RayPS/MacroPad/src/html.h

#ifndef HTML_H
#define HTML_H

#include <Arduino.h>

#define html_len 80776

const uint8_t html[] PROGMEM = {
0x1f,0x8b,0x08,0x00,0x00,0x00,0x00,0x00,0x02,0x13,0xcc,0xbd,0x69,0x73,0xdb,0xb8,0xd2,0x28,0xfc,0xfd,0xf9,0x15,0x91,0xca,0xa5,0x4b,0x3e,0x81,0x15,0x3b,0x93,0xc9,0xcc,0x50,0x86,0x55,0xde,0x12,0x3b,0xf1,0xbe,0x3b,0x1a,0x1d,0x1d,0x9a,0x82,0x25,0xda,0x12,0xc9,0x70,0x91,0x37,0xe9,0xfe,0xf6,0xdb,0xdd,0x58,0x08,0xca,0xca,0x3c,0xe7,0xde,0xaa,0xb7,0xea,0x9d,0x9a,0x58,0x24,0x88,0xb5,0xd1,0xe8,0x0d,0x8d,0xc6,0x5a,0x6d,0xfb,0x68,0xeb,0xfc,0xe6,0x78,0xe7,0xdd,0x30,0x1f,0x8f,0xd6,0xff,0x6b,0x0d,0x7f,0xde,0x8d,0xfc,0x68,0xc0,0xeb,0x22,0xaa,0xaf,0xff,0xd7,0xbb,0x77,0x6b,0x43,0xe1,0xf7,0xf1,0x01,0x1e,0xc7,0x22,0xf7,0xdf,0x05,0x43,0x3f,0xcd,0x44,0xce,0xeb,0x17,0xe7,0x5f,0x96,0xff,0xac,0xbf,0xfb,0x60,0x7f,0x8c,0xfc,0xb1,0xe0,0xf5,0x49,0x28,0x1e,0x93,0x38,0xcd,0xeb,0xef,0x82,0x38,0xca,0x45,0x04,0x99,0x1f,0xc3,0x7e,0x3e,0xe4,0x7d,0x31,0x09,0x03,0xb1,0x4c,0x2f,0xec,0x5d,0x18,0x85,0x79,0xe8,0x8f,0x96,0xb3,0xc0,0x1f,0x09,0xbe,0xda,0x5c,0x29,0x2b,0x1b,0x85,0xd1,0xc3,0xbb,0x54,0x8c,0x78,0x3d,0x1b,0x42,0x45,0x41,0x91,0xbf,0x0b,0xa1,0xae,0xfa,0xbb,0x61,0x2a,0xee,0x78,0xbd,0xef,0xe7,0xbe,0x17,0x8e,0xfd,0x81,0xf8,0x90,0x44,0x83,0xd6,0xad,0x9f,0x89,0xcf,0x9f,0x58,0x78,0xb9,0x79,0x74,0xfa,0xb8,0xf2,0xfd,0xeb,0x20,0xde,0x80,0xff,0x0e,0xcf,0x2e,0x86,0x3b,0x17,0x03,0x78,0xda,0xda,0xc1,0xf7,0xe1,0xd6,0xc6,0x09,0xfc,0x6c,0xff,0xf5,0xc7,0x49,0xfa,0x00,0x0f,0x9b,0xa3,0x95,0xd1,0xce,0xc9,0xe5,0xe9,0xa7,0x8f,0xc5,0xea,0xe5,0xc9,0xd5,0x1f,0x5b,0x07,0x9b,0xdb,0x07,0x1b,0x27,0x3b,0x1f,0xfc,0xdd,0x24,0x9f,0xfc,0xb5,0xfd,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
